kbjunky/Chordie/img/layers1.png

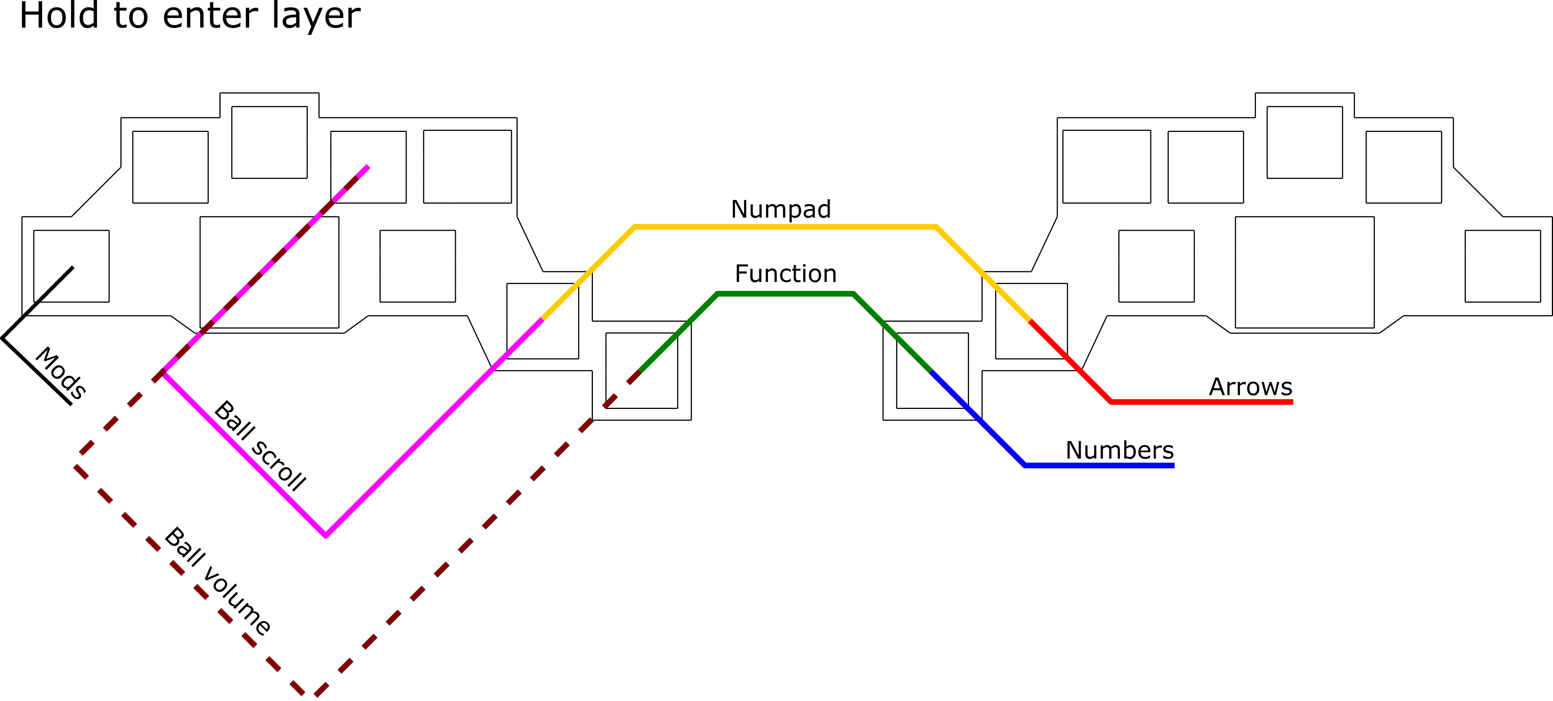
img/layers1.png
