kbjunky/Chordie/img/layers2.png

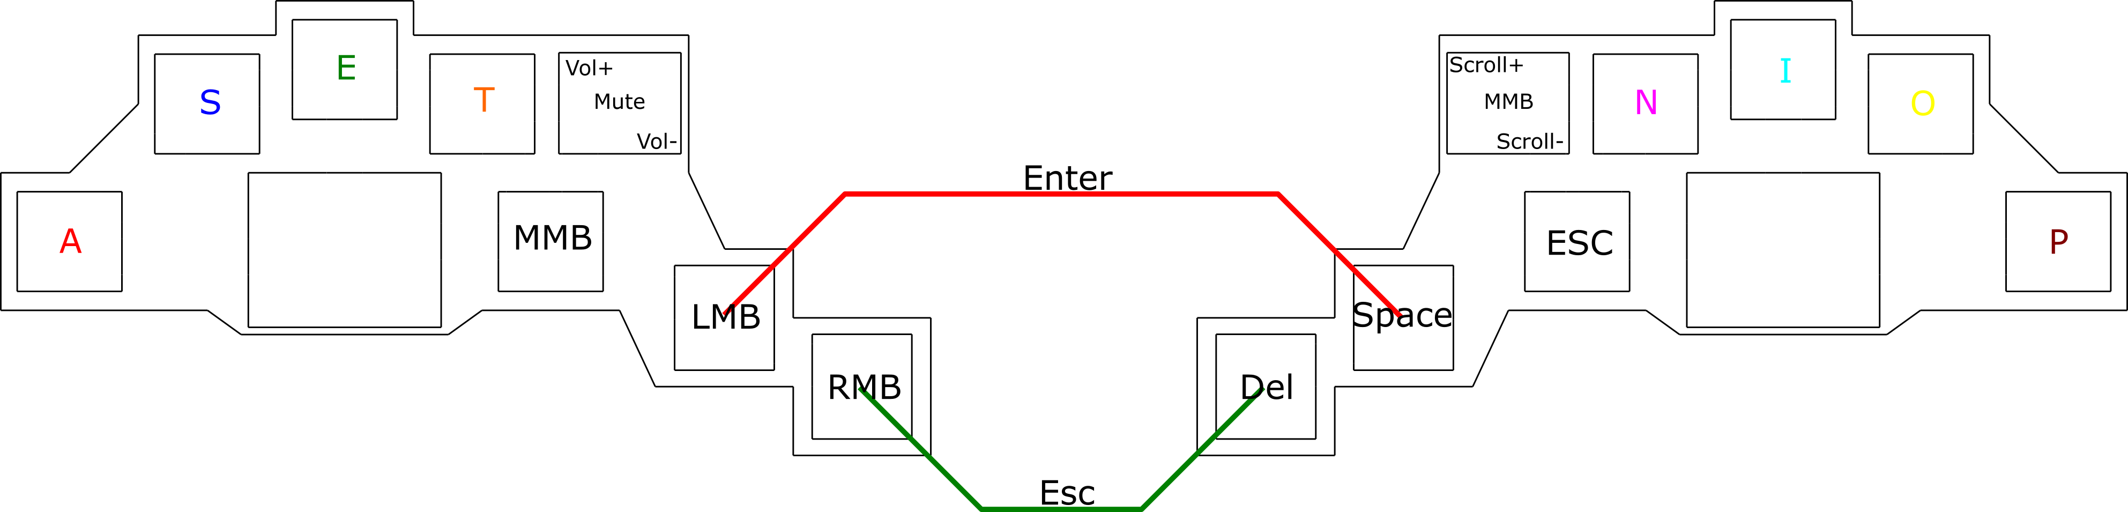
img/layers2.png
